eakat2/Checkers-Playing-Robot/Hardware/CAD/Board/Frames/Frame 2.SLDPRT

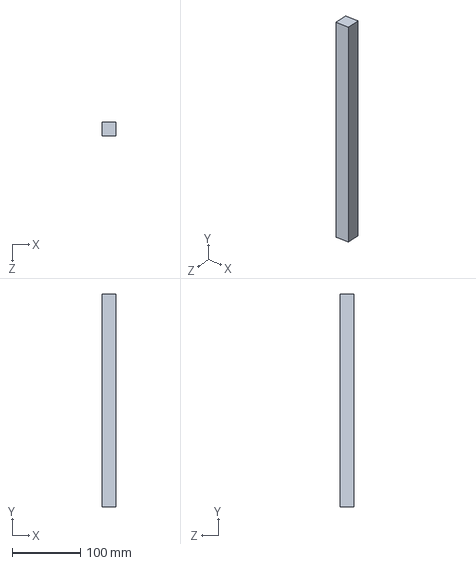
[picture p19: CAD file, 2021-05-21]
Hardware/CAD/Board/Frames/Frame 2.SLDPRT
20.0 x 311.0 x 20.0 mm
