eakat2/Checkers-Playing-Robot/Hardware/CAD/Board/Top.SLDPRT

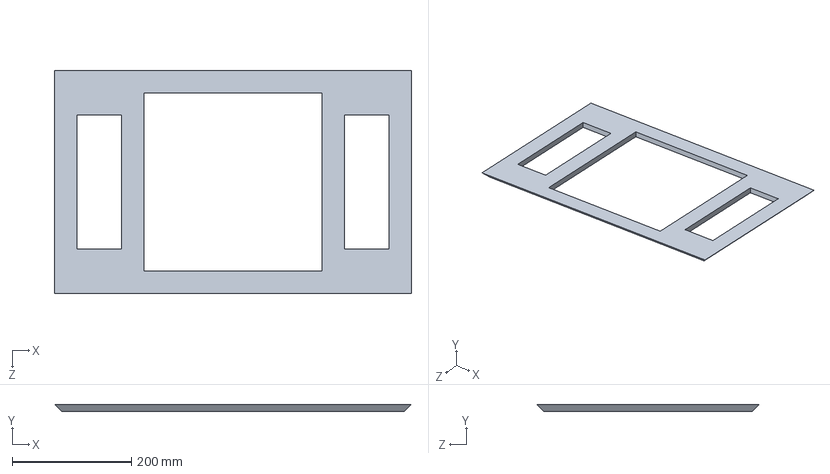
[picture p20: CAD file, 2021-05-21]
Hardware/CAD/Board/Top.SLDPRT
600.0 x 12.0 x 375.0 mm
