eakat2/Checkers-Playing-Robot/Hardware/CAD/Electromagnet.SLDPRT

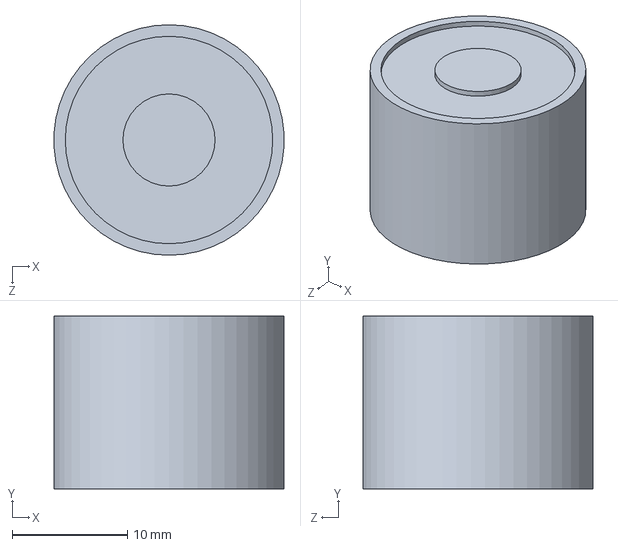
[picture p21: CAD file, 2021-01-19]
Hardware/CAD/Electromagnet.SLDPRT
20.0 x 15.0 x 20.0 mm
