eakat2/Checkers-Playing-Robot/Hardware/CAD/Arm/Base Bottom.SLDPRT

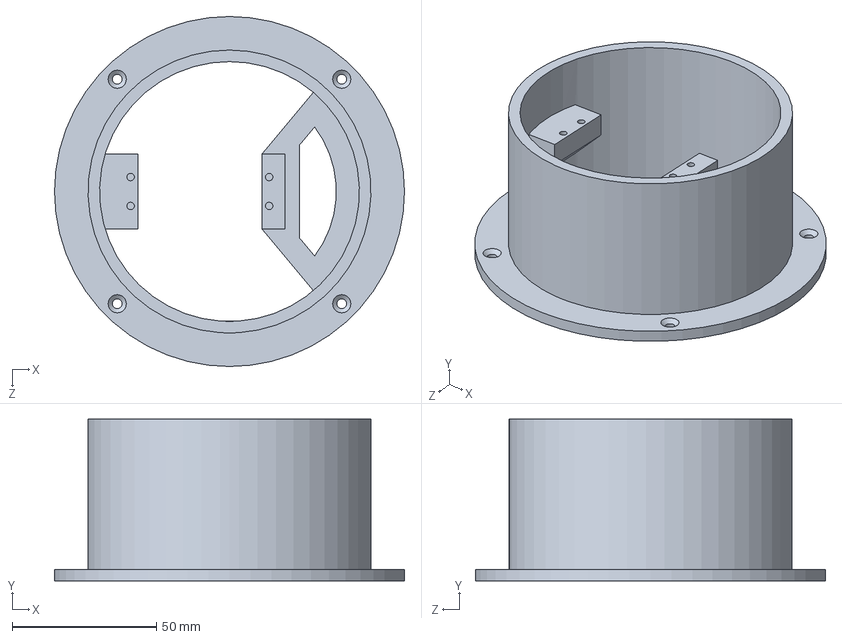
[picture p22: CAD file, 2021-05-28]
Hardware/CAD/Arm/Base Bottom.SLDPRT
121.2 x 56.0 x 121.2 mm
