eakat2/Checkers-Playing-Robot/Hardware/CAD/Arm/End Effector.SLDPRT

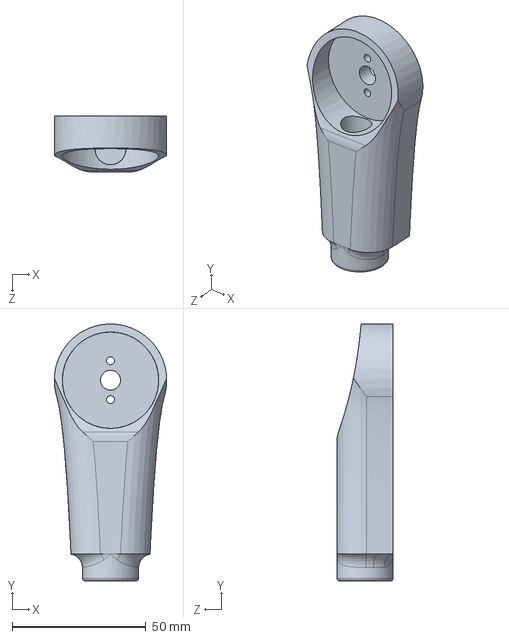
[picture p23: CAD file, 2021-05-28]
Hardware/CAD/Arm/End Effector.SLDPRT
42.0 x 96.0 x 21.0 mm
