eakat2/Checkers-Playing-Robot/Hardware/CAD/Board/Piece Draw.SLDPRT

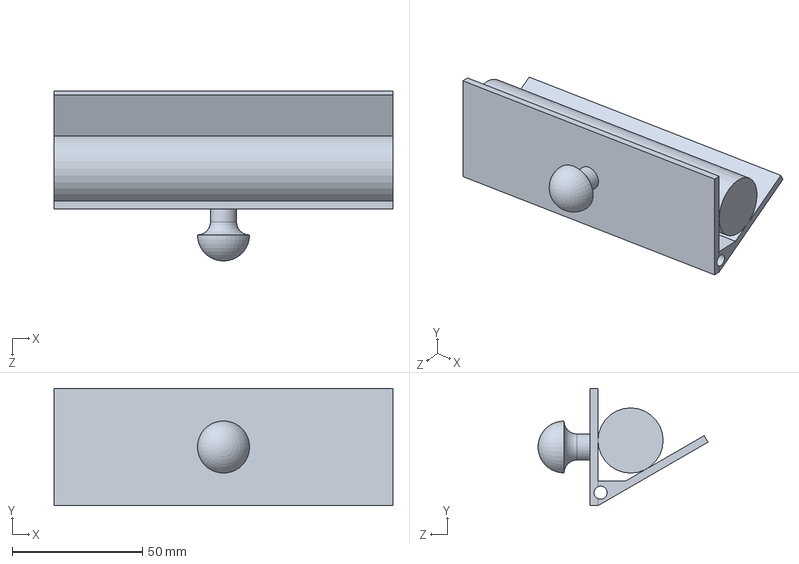
[picture p24: CAD file, 2021-05-21]
Hardware/CAD/Board/Piece Draw.SLDPRT
130.0 x 45.0 x 65.2 mm
