eakat2/Checkers-Playing-Robot/Hardware/CAD/Raspberry Pi/Microphone Plug, RPi4ModelB.SLDPRT

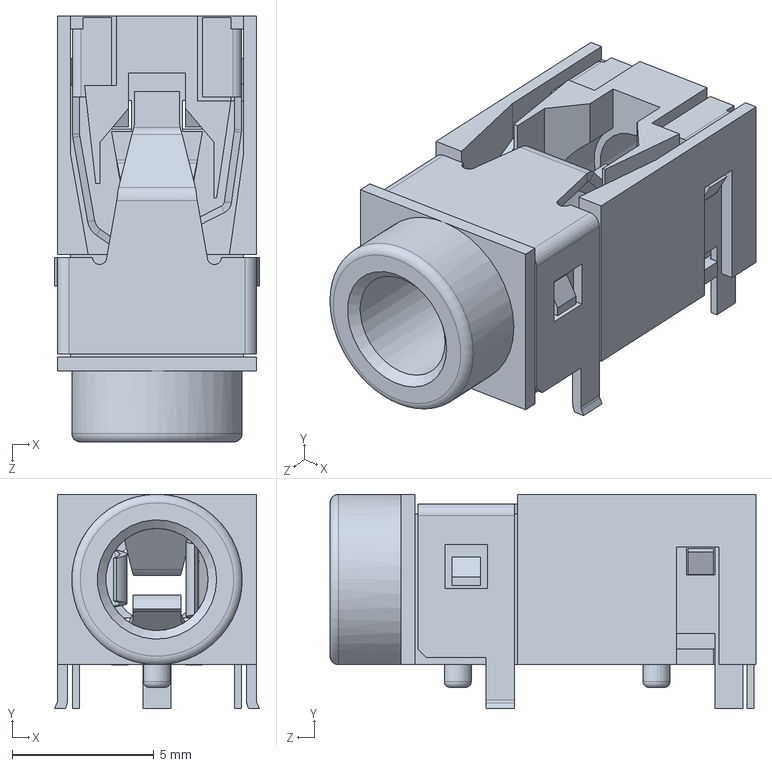
[picture p25: CAD file, 2021-01-19]
Hardware/CAD/Raspberry Pi/Microphone Plug, RPi4ModelB.SLDPRT
7.23 x 7.55 x 15.0 mm
