eakat2/Checkers-Playing-Robot/Hardware/CAD/Board/Front.SLDPRT

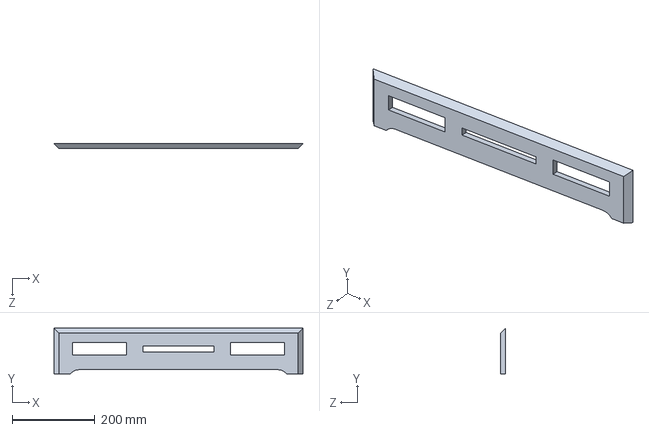
[picture p26: CAD file, 2021-05-21]
Hardware/CAD/Board/Front.SLDPRT
600.0 x 110.0 x 12.0 mm
