eakat2/Checkers-Playing-Robot/Hardware/CAD/Raspberry Pi/2.54 mm DUPONT MALE PIN HEADER, POE, 2X2, RPi4ModelB.SLDPRT

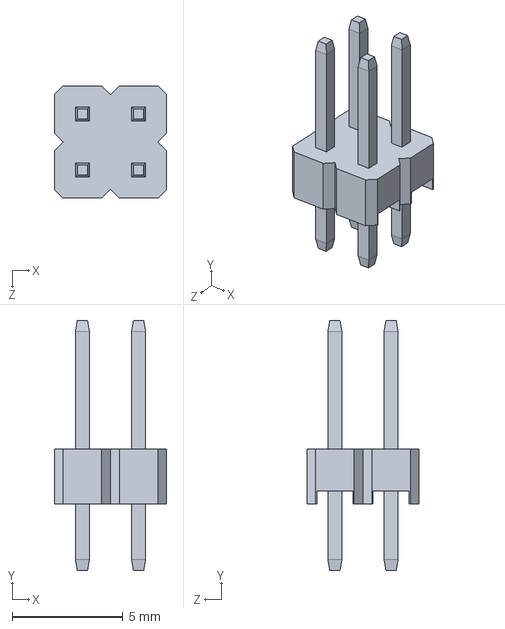
[picture p27: CAD file, 2021-01-19]
Hardware/CAD/Raspberry Pi/2.54 mm DUPONT MALE PIN HEADER, POE, 2X2, RPi4ModelB.SLDPRT
5.08 x 11.3 x 5.08 mm
