eakat2/Checkers-Playing-Robot/Hardware/CAD/Arm/Part 2.SLDPRT

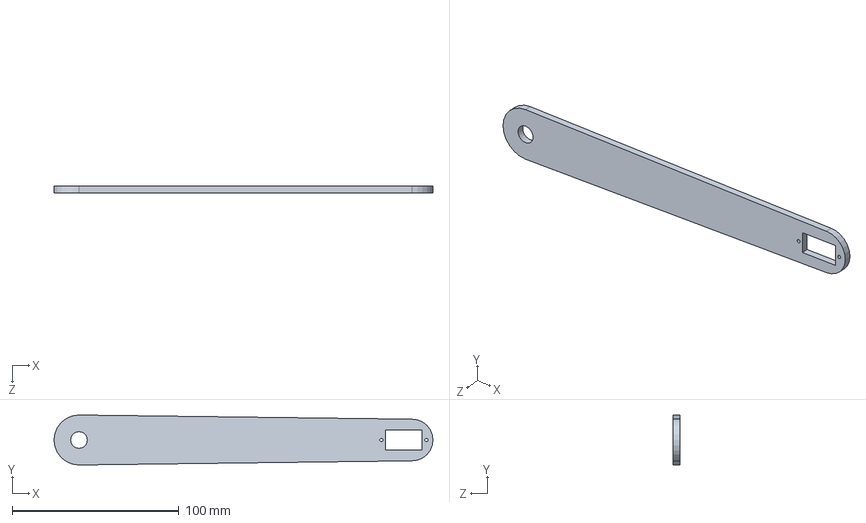
[picture p28: CAD file, 2021-05-21]
Hardware/CAD/Arm/Part 2.SLDPRT
227.5 x 30.0 x 4.00 mm
