eakat2/Checkers-Playing-Robot/Hardware/CAD/Board/Back.SLDPRT

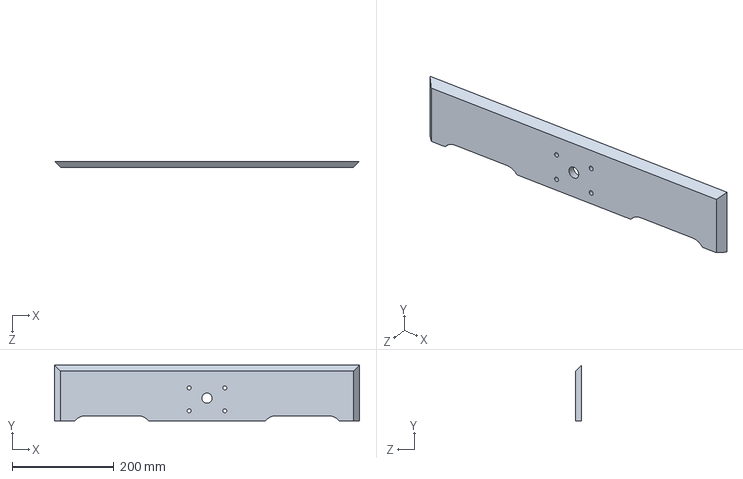
[picture p29: CAD file, 2021-05-21]
Hardware/CAD/Board/Back.SLDPRT
600.0 x 110.0 x 12.0 mm
