eakat2/Checkers-Playing-Robot/Hardware/CAD/Raspberry Pi/Female USB Type C Connector, RPi4ModelB.SLDPRT

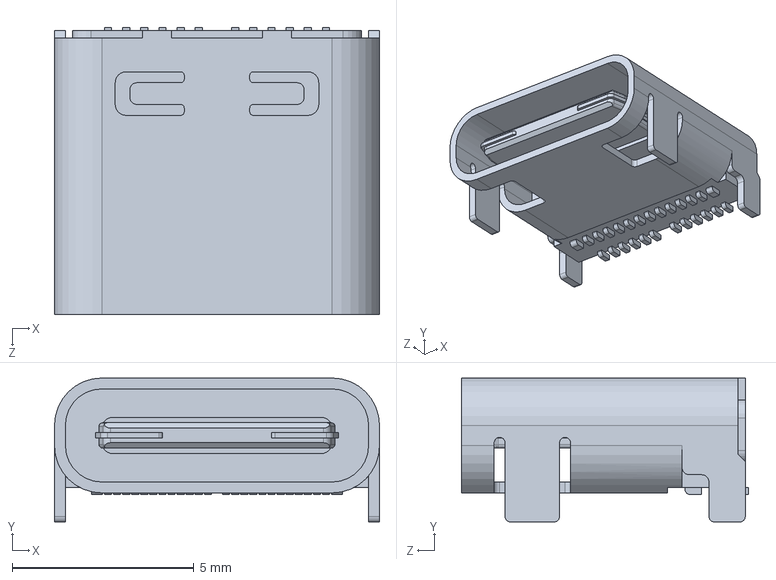
[picture p30: CAD file, 2021-01-19]
Hardware/CAD/Raspberry Pi/Female USB Type C Connector, RPi4ModelB.SLDPRT
8.94 x 3.96 x 7.90 mm
