eakat2/Checkers-Playing-Robot/Hardware/CAD/Arm/Base Top.SLDPRT

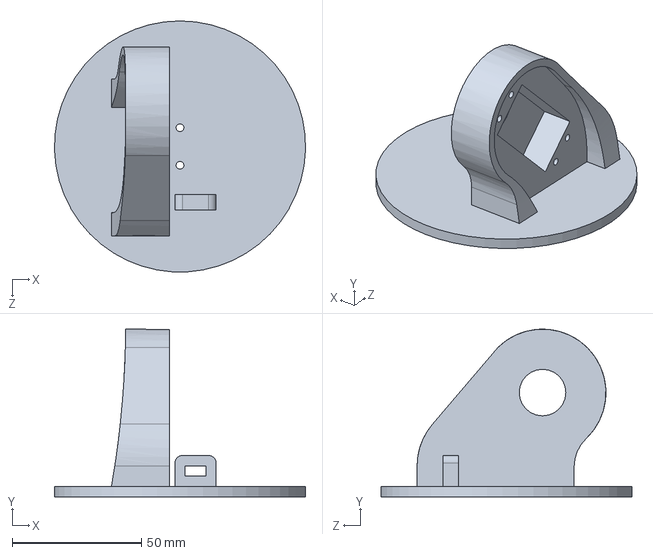
[picture p31: CAD file, 2021-05-21]
Hardware/CAD/Arm/Base Top.SLDPRT
97.0 x 64.8 x 97.0 mm
