eakat2/Checkers-Playing-Robot/Hardware/CAD/Raspberry Pi/2X USB2.0 PORTS, RPi4ModelB.SLDPRT

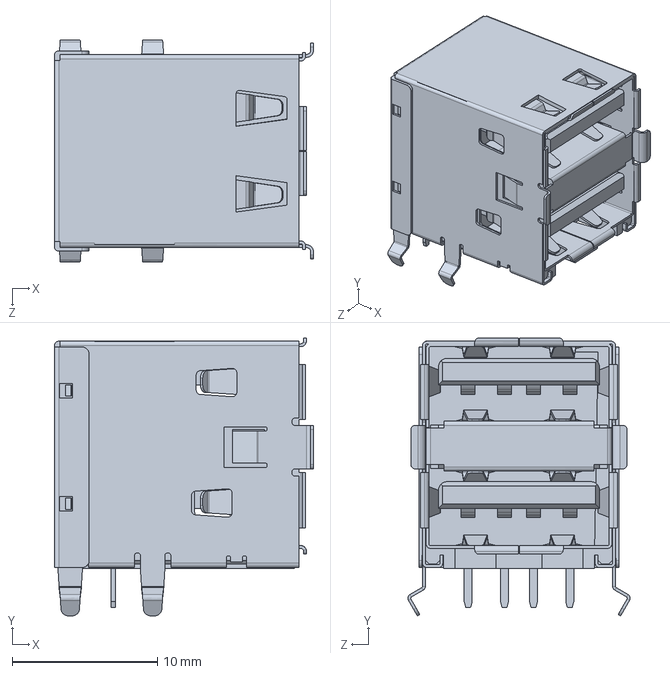
[picture p32: CAD file, 2021-01-19]
Hardware/CAD/Raspberry Pi/2X USB2.0 PORTS, RPi4ModelB.SLDPRT
17.9 x 19.2 x 15.3 mm
