eakat2/Checkers-Playing-Robot/Hardware/CAD/Arm/Part 4.SLDPRT

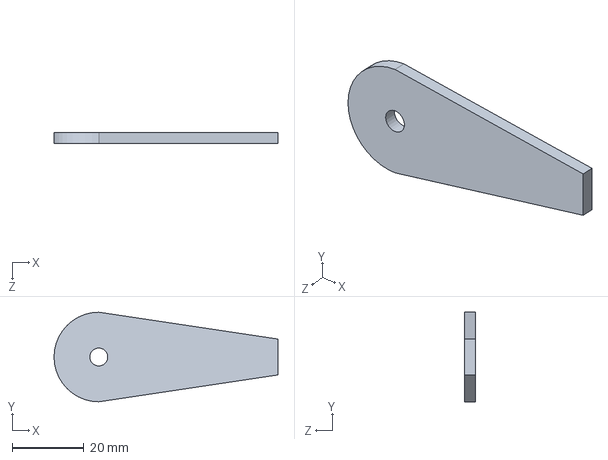
[picture p33: CAD file, 2021-05-21]
Hardware/CAD/Arm/Part 4.SLDPRT
62.5 x 25.0 x 3.00 mm
