eakat2/Checkers-Playing-Robot/Hardware/CAD/Raspberry Pi/Broadcom BCM54213PE Gigabit Ethernet Transceiver, RPi4ModelB.SLDPRT

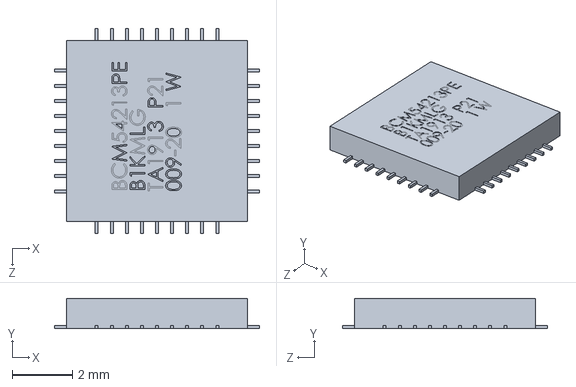
[picture p34: CAD file, 2021-01-19]
Hardware/CAD/Raspberry Pi/Broadcom BCM54213PE Gigabit Ethernet Transceiver, RPi4ModelB.SLDPRT
6.80 x 1.00 x 6.80 mm
