eakat2/Checkers-Playing-Robot/Hardware/CAD/Arm/Part 3.SLDPRT

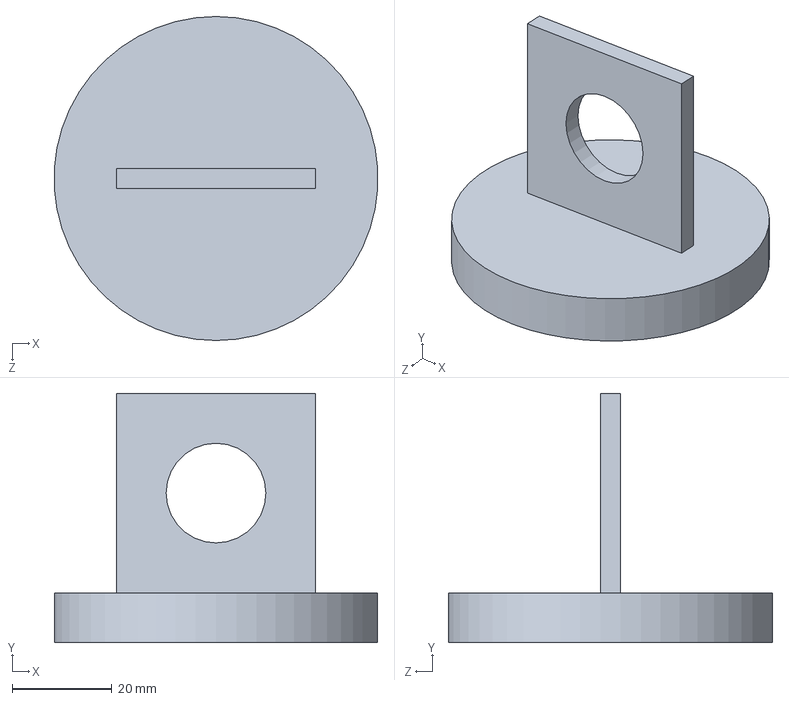
[picture p35: CAD file, 2021-05-21]
Hardware/CAD/Arm/Part 3.SLDPRT
64.9 x 50.0 x 65.0 mm
