eakat2/Checkers-Playing-Robot/Hardware/CAD/Arm/Part 1.SLDPRT

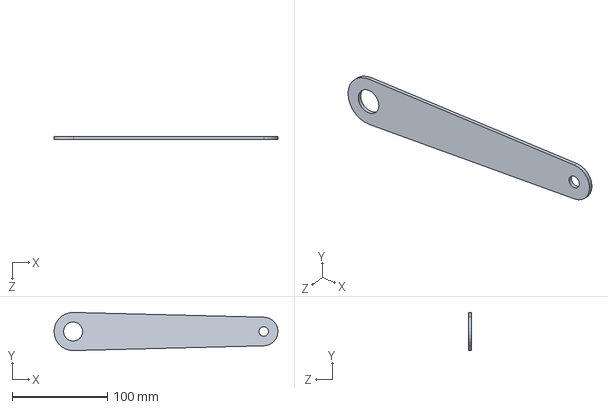
[picture p36: CAD file, 2021-05-21]
Hardware/CAD/Arm/Part 1.SLDPRT
235.0 x 40.0 x 3.00 mm
