eakat2/Checkers-Playing-Robot/Hardware/CAD/Raspberry Pi/2X USB3.0 PORTS, RPi4ModelB.SLDPRT

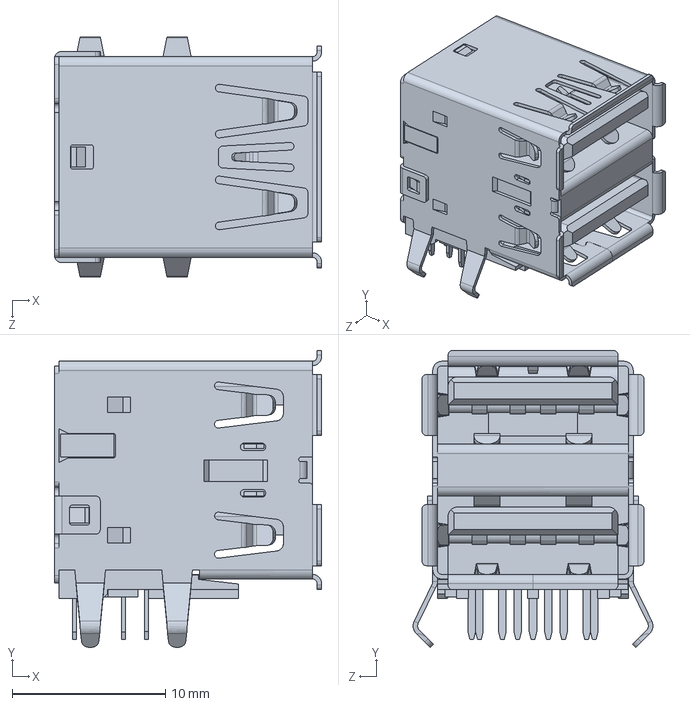
[picture p37: CAD file, 2021-01-19]
Hardware/CAD/Raspberry Pi/2X USB3.0 PORTS, RPi4ModelB.SLDPRT
17.5 x 19.4 x 15.7 mm
