eakat2/Checkers-Playing-Robot/Hardware/CAD/Arm/Spacer.SLDPRT

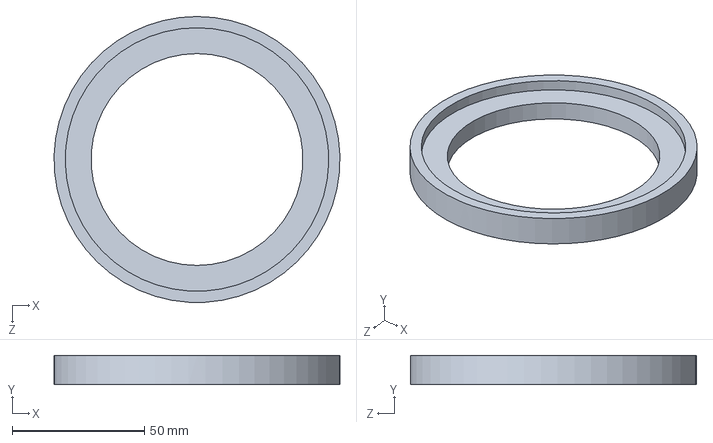
[picture p38: CAD file, 2021-05-21]
Hardware/CAD/Arm/Spacer.SLDPRT
108.0 x 11.0 x 108.0 mm
