eakat2/Checkers-Playing-Robot/Hardware/CAD/Arm/Arm Box.SLDPRT

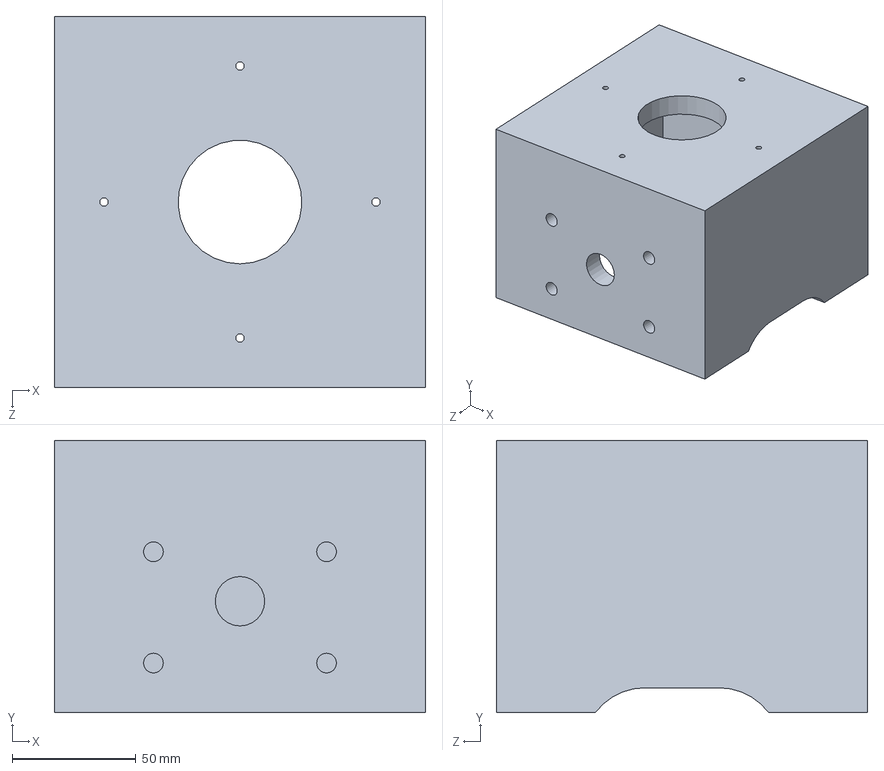
[picture p39: CAD file, 2021-05-21]
Hardware/CAD/Arm/Arm Box.SLDPRT
150.0 x 110.0 x 150.0 mm
