eakat2/Checkers-Playing-Robot/Hardware/CAD/Raspberry Pi/Cypress CYW43455 Wireless Module Cover, RPi4ModelB.SLDPRT

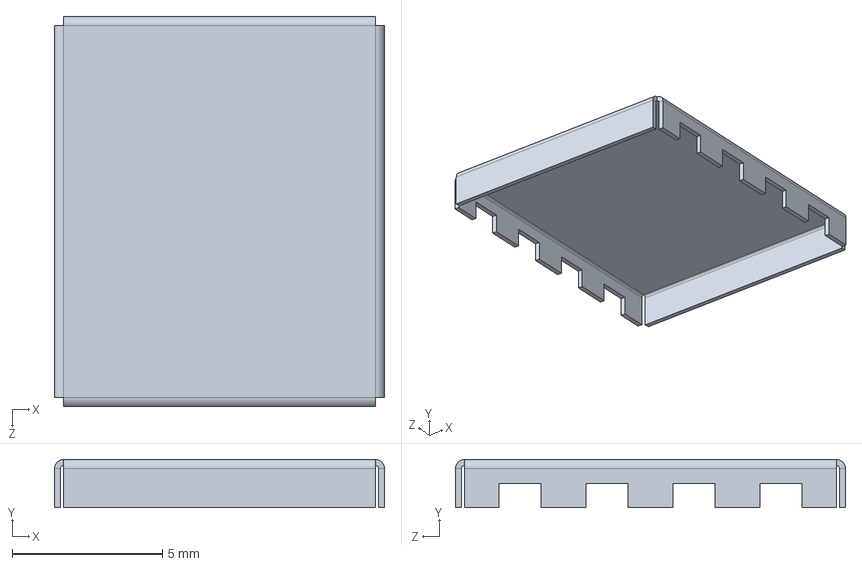
[picture p40: CAD file, 2021-01-19]
Hardware/CAD/Raspberry Pi/Cypress CYW43455 Wireless Module Cover, RPi4ModelB.SLDPRT
11.0 x 1.60 x 13.0 mm
