eakat2/Checkers-Playing-Robot/Hardware/CAD/Raspberry Pi/VIA VL805 PCIe USB 3.0 controller, RPi4ModelB.SLDPRT

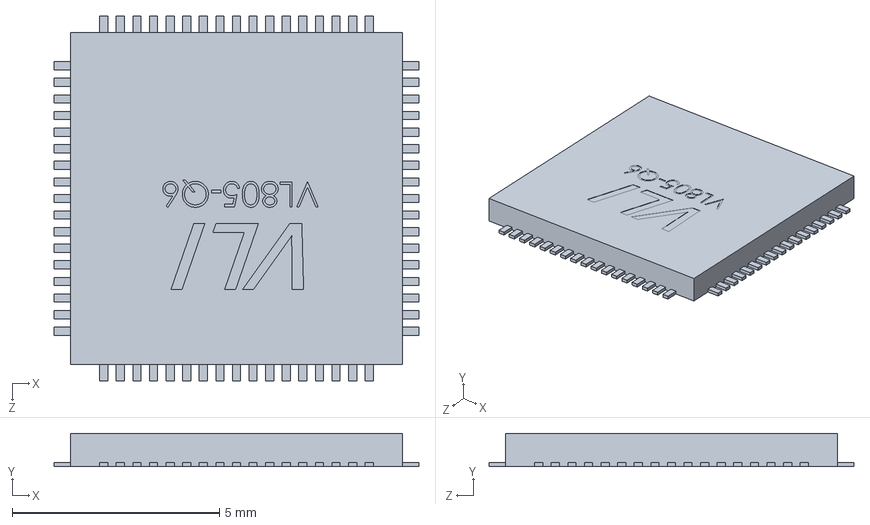
[picture p41: CAD file, 2021-01-19]
Hardware/CAD/Raspberry Pi/VIA VL805 PCIe USB 3.0 controller, RPi4ModelB.SLDPRT
8.80 x 0.8 x 8.80 mm
