eakat2/Checkers-Playing-Robot/Hardware/CAD/Raspberry Pi/Female Micro HDMI Connector, RPi4ModelB.SLDPRT

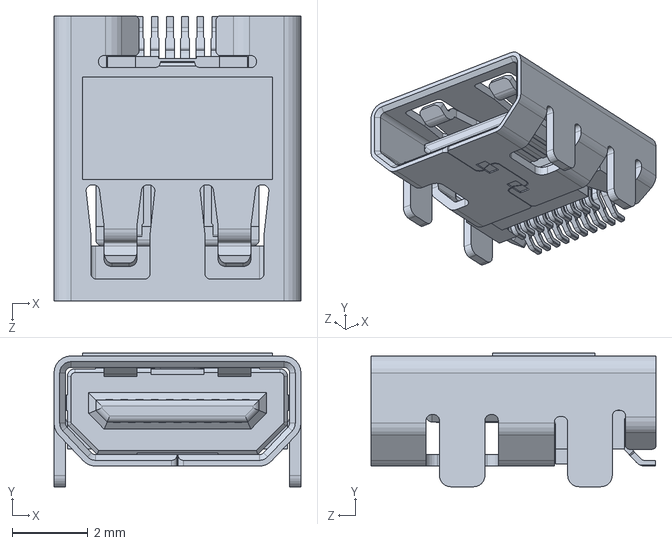
[picture p42: CAD file, 2021-01-19]
Hardware/CAD/Raspberry Pi/Female Micro HDMI Connector, RPi4ModelB.SLDPRT
6.50 x 3.52 x 7.50 mm
