eakat2/Checkers-Playing-Robot/Movement System/Game Piece Movement System.cydsn/codegentemp/Servo_4.h

/*******************************************************************************
* File Name: Servo_4.h  
* Version 2.20
*
* Description:
*  This file contains Pin function prototypes and register defines
*
* Note:
*
********************************************************************************
* Copyright 2008-2015, Cypress Semiconductor Corporation.  All rights reserved.
* You may use this file only in accordance with the license, terms, conditions, 
* disclaimers, and limitations in the end user license agreement accompanying 
* the software package with which this file was provided.
*******************************************************************************/

#if !defined(CY_PINS_Servo_4_H) /* Pins Servo_4_H */
#define CY_PINS_Servo_4_H

#include "cytypes.h"
#include "cyfitter.h"
#include "cypins.h"
#include "Servo_4_aliases.h"

/* APIs are not generated for P15[7:6] */
#if !(CY_PSOC5A &&\
	 Servo_4__PORT == 15 && ((Servo_4__MASK & 0xC0) != 0))


/***************************************
*        Function Prototypes             
***************************************/    

/**
* \addtogroup group_general
* @{
*/
void    Servo_4_Write(uint8 value);
void    Servo_4_SetDriveMode(uint8 mode);
uint8   Servo_4_ReadDataReg(void);
uint8   Servo_4_Read(void);
void    Servo_4_SetInterruptMode(uint16 position, uint16 mode);
uint8   Servo_4_ClearInterrupt(void);
/** @} general */

/***************************************
*           API Constants        
***************************************/
/**
* \addtogroup group_constants
* @{
*/
    /** \addtogroup driveMode Drive mode constants
     * \brief Constants to be passed as "mode" parameter in the Servo_4_SetDriveMode() function.
     *  @{
     */
        #define Servo_4_DM_ALG_HIZ         PIN_DM_ALG_HIZ
        #define Servo_4_DM_DIG_HIZ         PIN_DM_DIG_HIZ
        #define Servo_4_DM_RES_UP          PIN_DM_RES_UP
        #define Servo_4_DM_RES_DWN         PIN_DM_RES_DWN
        #define Servo_4_DM_OD_LO           PIN_DM_OD_LO
        #define Servo_4_DM_OD_HI           PIN_DM_OD_HI
        #define Servo_4_DM_STRONG          PIN_DM_STRONG
        #define Servo_4_DM_RES_UPDWN       PIN_DM_RES_UPDWN
    /** @} driveMode */
/** @} group_constants */
    
/* Digital Port Constants */
#define Servo_4_MASK               Servo_4__MASK
#define Servo_4_SHIFT              Servo_4__SHIFT
#define Servo_4_WIDTH              1u

/* Interrupt constants */
#if defined(Servo_4__INTSTAT)
/**
* \addtogroup group_constants
* @{
*/
    /** \addtogroup intrMode Interrupt constants
     * \brief Constants to be passed as "mode" parameter in Servo_4_SetInterruptMode() function.
     *  @{
     */
        #define Servo_4_INTR_NONE      (uint16)(0x0000u)
        #define Servo_4_INTR_RISING    (uint16)(0x0001u)
        #define Servo_4_INTR_FALLING   (uint16)(0x0002u)
        #define Servo_4_INTR_BOTH      (uint16)(0x0003u) 
    /** @} intrMode */
/** @} group_constants */

    #define Servo_4_INTR_MASK      (0x01u) 
#endif /* (Servo_4__INTSTAT) */


/***************************************
*             Registers        
***************************************/

/* Main Port Registers */
/* Pin State */
#define Servo_4_PS                     (* (reg8 *) Servo_4__PS)
/* Data Register */
#define Servo_4_DR                     (* (reg8 *) Servo_4__DR)
/* Port Number */
#define Servo_4_PRT_NUM                (* (reg8 *) Servo_4__PRT) 
/* Connect to Analog Globals */                                                  
#define Servo_4_AG                     (* (reg8 *) Servo_4__AG)                       
/* Analog MUX bux enable */
#define Servo_4_AMUX                   (* (reg8 *) Servo_4__AMUX) 
/* Bidirectional Enable */                                                        
#define Servo_4_BIE                    (* (reg8 *) Servo_4__BIE)
/* Bit-mask for Aliased Register Access */
#define Servo_4_BIT_MASK               (* (reg8 *) Servo_4__BIT_MASK)
/* Bypass Enable */
#define Servo_4_BYP                    (* (reg8 *) Servo_4__BYP)
/* Port wide control signals */                                                   
#define Servo_4_CTL                    (* (reg8 *) Servo_4__CTL)
/* Drive Modes */
#define Servo_4_DM0                    (* (reg8 *) Servo_4__DM0) 
#define Servo_4_DM1                    (* (reg8 *) Servo_4__DM1)
#define Servo_4_DM2                    (* (reg8 *) Servo_4__DM2) 
/* Input Buffer Disable Override */
#define Servo_4_INP_DIS                (* (reg8 *) Servo_4__INP_DIS)
/* LCD Common or Segment Drive */
#define Servo_4_LCD_COM_SEG            (* (reg8 *) Servo_4__LCD_COM_SEG)
/* Enable Segment LCD */
#define Servo_4_LCD_EN                 (* (reg8 *) Servo_4__LCD_EN)
/* Slew Rate Control */
#define Servo_4_SLW                    (* (reg8 *) Servo_4__SLW)

/* DSI Port Registers */
/* Global DSI Select Register */
#define Servo_4_PRTDSI__CAPS_SEL       (* (reg8 *) Servo_4__PRTDSI__CAPS_SEL) 
/* Double Sync Enable */
#define Servo_4_PRTDSI__DBL_SYNC_IN    (* (reg8 *) Servo_4__PRTDSI__DBL_SYNC_IN) 
/* Output Enable Select Drive Strength */
#define Servo_4_PRTDSI__OE_SEL0        (* (reg8 *) Servo_4__PRTDSI__OE_SEL0) 
#define Servo_4_PRTDSI__OE_SEL1        (* (reg8 *) Servo_4__PRTDSI__OE_SEL1) 
/* Port Pin Output Select Registers */
#define Servo_4_PRTDSI__OUT_SEL0       (* (reg8 *) Servo_4__PRTDSI__OUT_SEL0) 
#define Servo_4_PRTDSI__OUT_SEL1       (* (reg8 *) Servo_4__PRTDSI__OUT_SEL1) 
/* Sync Output Enable Registers */
#define Servo_4_PRTDSI__SYNC_OUT       (* (reg8 *) Servo_4__PRTDSI__SYNC_OUT) 

/* SIO registers */
#if defined(Servo_4__SIO_CFG)
    #define Servo_4_SIO_HYST_EN        (* (reg8 *) Servo_4__SIO_HYST_EN)
    #define Servo_4_SIO_REG_HIFREQ     (* (reg8 *) Servo_4__SIO_REG_HIFREQ)
    #define Servo_4_SIO_CFG            (* (reg8 *) Servo_4__SIO_CFG)
    #define Servo_4_SIO_DIFF           (* (reg8 *) Servo_4__SIO_DIFF)
#endif /* (Servo_4__SIO_CFG) */

/* Interrupt Registers */
#if defined(Servo_4__INTSTAT)
    #define Servo_4_INTSTAT            (* (reg8 *) Servo_4__INTSTAT)
    #define Servo_4_SNAP               (* (reg8 *) Servo_4__SNAP)
    
	#define Servo_4_0_INTTYPE_REG 		(* (reg8 *) Servo_4__0__INTTYPE)
#endif /* (Servo_4__INTSTAT) */

#endif /* CY_PSOC5A... */

#endif /*  CY_PINS_Servo_4_H */


/* [] END OF FILE */
