eakat2/Checkers-Playing-Robot/Movement System/Game Piece Movement System.cydsn/codegentemp/Servo_1_aliases.h

/*******************************************************************************
* File Name: Servo_1.h  
* Version 2.20
*
* Description:
*  This file contains the Alias definitions for Per-Pin APIs in cypins.h. 
*  Information on using these APIs can be found in the System Reference Guide.
*
* Note:
*
********************************************************************************
* Copyright 2008-2015, Cypress Semiconductor Corporation.  All rights reserved.
* You may use this file only in accordance with the license, terms, conditions, 
* disclaimers, and limitations in the end user license agreement accompanying 
* the software package with which this file was provided.
*******************************************************************************/

#if !defined(CY_PINS_Servo_1_ALIASES_H) /* Pins Servo_1_ALIASES_H */
#define CY_PINS_Servo_1_ALIASES_H

#include "cytypes.h"
#include "cyfitter.h"


/***************************************
*              Constants        
***************************************/
#define Servo_1_0			(Servo_1__0__PC)
#define Servo_1_0_INTR	((uint16)((uint16)0x0001u << Servo_1__0__SHIFT))

#define Servo_1_INTR_ALL	 ((uint16)(Servo_1_0_INTR))

#endif /* End Pins Servo_1_ALIASES_H */


/* [] END OF FILE */
