eakat2/Checkers-Playing-Robot/Movement System/Game Piece Movement System.cydsn/codegentemp/PWM_1.h

/*******************************************************************************
* File Name: PWM_1.h
* Version 3.30
*
* Description:
*  Contains the prototypes and constants for the functions available to the
*  PWM user module.
*
* Note:
*
********************************************************************************
* Copyright 2008-2014, Cypress Semiconductor Corporation.  All rights reserved.
* You may use this file only in accordance with the license, terms, conditions,
* disclaimers, and limitations in the end user license agreement accompanying
* the software package with which this file was provided.
********************************************************************************/

#if !defined(CY_PWM_PWM_1_H)
#define CY_PWM_PWM_1_H

#include "cyfitter.h"
#include "cytypes.h"
#include "CyLib.h" /* For CyEnterCriticalSection() and CyExitCriticalSection() functions */

extern uint8 PWM_1_initVar;


/***************************************
* Conditional Compilation Parameters
***************************************/
#define PWM_1_Resolution                     (16u)
#define PWM_1_UsingFixedFunction             (0u)
#define PWM_1_DeadBandMode                   (0u)
#define PWM_1_KillModeMinTime                (0u)
#define PWM_1_KillMode                       (0u)
#define PWM_1_PWMMode                        (0u)
#define PWM_1_PWMModeIsCenterAligned         (0u)
#define PWM_1_DeadBandUsed                   (0u)
#define PWM_1_DeadBand2_4                    (0u)

#if !defined(PWM_1_PWMUDB_genblk8_stsreg__REMOVED)
    #define PWM_1_UseStatus                  (1u)
#else
    #define PWM_1_UseStatus                  (0u)
#endif /* !defined(PWM_1_PWMUDB_genblk8_stsreg__REMOVED) */

#if !defined(PWM_1_PWMUDB_genblk1_ctrlreg__REMOVED)
    #define PWM_1_UseControl                 (1u)
#else
    #define PWM_1_UseControl                 (0u)
#endif /* !defined(PWM_1_PWMUDB_genblk1_ctrlreg__REMOVED) */

#define PWM_1_UseOneCompareMode              (1u)
#define PWM_1_MinimumKillTime                (1u)
#define PWM_1_EnableMode                     (0u)

#define PWM_1_CompareMode1SW                 (0u)
#define PWM_1_CompareMode2SW                 (0u)

/* Check to see if required defines such as CY_PSOC5LP are available */
/* They are defined starting with cy_boot v3.0 */
#if !defined (CY_PSOC5LP)
    #error Component PWM_v3_30 requires cy_boot v3.0 or later
#endif /* (CY_ PSOC5LP) */

/* Use Kill Mode Enumerated Types */
#define PWM_1__B_PWM__DISABLED 0
#define PWM_1__B_PWM__ASYNCHRONOUS 1
#define PWM_1__B_PWM__SINGLECYCLE 2
#define PWM_1__B_PWM__LATCHED 3
#define PWM_1__B_PWM__MINTIME 4


/* Use Dead Band Mode Enumerated Types */
#define PWM_1__B_PWM__DBMDISABLED 0
#define PWM_1__B_PWM__DBM_2_4_CLOCKS 1
#define PWM_1__B_PWM__DBM_256_CLOCKS 2


/* Used PWM Mode Enumerated Types */
#define PWM_1__B_PWM__ONE_OUTPUT 0
#define PWM_1__B_PWM__TWO_OUTPUTS 1
#define PWM_1__B_PWM__DUAL_EDGE 2
#define PWM_1__B_PWM__CENTER_ALIGN 3
#define PWM_1__B_PWM__DITHER 5
#define PWM_1__B_PWM__HARDWARESELECT 4


/* Used PWM Compare Mode Enumerated Types */
#define PWM_1__B_PWM__LESS_THAN 1
#define PWM_1__B_PWM__LESS_THAN_OR_EQUAL 2
#define PWM_1__B_PWM__GREATER_THAN 3
#define PWM_1__B_PWM__GREATER_THAN_OR_EQUAL_TO 4
#define PWM_1__B_PWM__EQUAL 0
#define PWM_1__B_PWM__FIRMWARE 5



/***************************************
* Data Struct Definition
***************************************/


/**************************************************************************
 * Sleep Wakeup Backup structure for PWM Component
 *************************************************************************/
typedef struct
{

    uint8 PWMEnableState;

    #if(!PWM_1_UsingFixedFunction)
        uint16 PWMUdb;               /* PWM Current Counter value  */
        #if(!PWM_1_PWMModeIsCenterAligned)
            uint16 PWMPeriod;
        #endif /* (!PWM_1_PWMModeIsCenterAligned) */
        #if (PWM_1_UseStatus)
            uint8 InterruptMaskValue;   /* PWM Current Interrupt Mask */
        #endif /* (PWM_1_UseStatus) */

        /* Backup for Deadband parameters */
        #if(PWM_1_DeadBandMode == PWM_1__B_PWM__DBM_256_CLOCKS || \
            PWM_1_DeadBandMode == PWM_1__B_PWM__DBM_2_4_CLOCKS)
            uint8 PWMdeadBandValue; /* Dead Band Counter Current Value */
        #endif /* deadband count is either 2-4 clocks or 256 clocks */

        /* Backup Kill Mode Counter*/
        #if(PWM_1_KillModeMinTime)
            uint8 PWMKillCounterPeriod; /* Kill Mode period value */
        #endif /* (PWM_1_KillModeMinTime) */

        /* Backup control register */
        #if(PWM_1_UseControl)
            uint8 PWMControlRegister; /* PWM Control Register value */
        #endif /* (PWM_1_UseControl) */

    #endif /* (!PWM_1_UsingFixedFunction) */

}PWM_1_backupStruct;


/***************************************
*        Function Prototypes
 **************************************/

void    PWM_1_Start(void) ;
void    PWM_1_Stop(void) ;

#if (PWM_1_UseStatus || PWM_1_UsingFixedFunction)
    void  PWM_1_SetInterruptMode(uint8 interruptMode) ;
    uint8 PWM_1_ReadStatusRegister(void) ;
#endif /* (PWM_1_UseStatus || PWM_1_UsingFixedFunction) */

#define PWM_1_GetInterruptSource() PWM_1_ReadStatusRegister()

#if (PWM_1_UseControl)
    uint8 PWM_1_ReadControlRegister(void) ;
    void  PWM_1_WriteControlRegister(uint8 control)
          ;
#endif /* (PWM_1_UseControl) */

#if (PWM_1_UseOneCompareMode)
   #if (PWM_1_CompareMode1SW)
       void    PWM_1_SetCompareMode(uint8 comparemode)
               ;
   #endif /* (PWM_1_CompareMode1SW) */
#else
    #if (PWM_1_CompareMode1SW)
        void    PWM_1_SetCompareMode1(uint8 comparemode)
                ;
    #endif /* (PWM_1_CompareMode1SW) */
    #if (PWM_1_CompareMode2SW)
        void    PWM_1_SetCompareMode2(uint8 comparemode)
                ;
    #endif /* (PWM_1_CompareMode2SW) */
#endif /* (PWM_1_UseOneCompareMode) */

#if (!PWM_1_UsingFixedFunction)
    uint16   PWM_1_ReadCounter(void) ;
    uint16 PWM_1_ReadCapture(void) ;

    #if (PWM_1_UseStatus)
            void PWM_1_ClearFIFO(void) ;
    #endif /* (PWM_1_UseStatus) */

    void    PWM_1_WriteCounter(uint16 counter)
            ;
#endif /* (!PWM_1_UsingFixedFunction) */

void    PWM_1_WritePeriod(uint16 period)
        ;
uint16 PWM_1_ReadPeriod(void) ;

#if (PWM_1_UseOneCompareMode)
    void    PWM_1_WriteCompare(uint16 compare)
            ;
    uint16 PWM_1_ReadCompare(void) ;
#else
    void    PWM_1_WriteCompare1(uint16 compare)
            ;
    uint16 PWM_1_ReadCompare1(void) ;
    void    PWM_1_WriteCompare2(uint16 compare)
            ;
    uint16 PWM_1_ReadCompare2(void) ;
#endif /* (PWM_1_UseOneCompareMode) */


#if (PWM_1_DeadBandUsed)
    void    PWM_1_WriteDeadTime(uint8 deadtime) ;
    uint8   PWM_1_ReadDeadTime(void) ;
#endif /* (PWM_1_DeadBandUsed) */

#if ( PWM_1_KillModeMinTime)
    void PWM_1_WriteKillTime(uint8 killtime) ;
    uint8 PWM_1_ReadKillTime(void) ;
#endif /* ( PWM_1_KillModeMinTime) */

void PWM_1_Init(void) ;
void PWM_1_Enable(void) ;
void PWM_1_Sleep(void) ;
void PWM_1_Wakeup(void) ;
void PWM_1_SaveConfig(void) ;
void PWM_1_RestoreConfig(void) ;


/***************************************
*         Initialization Values
**************************************/
#define PWM_1_INIT_PERIOD_VALUE          (39999u)
#define PWM_1_INIT_COMPARE_VALUE1        (2000u)
#define PWM_1_INIT_COMPARE_VALUE2        (63u)
#define PWM_1_INIT_INTERRUPTS_MODE       (uint8)(((uint8)(0u <<   \
                                                    PWM_1_STATUS_TC_INT_EN_MASK_SHIFT)) | \
                                                    (uint8)((uint8)(0u <<  \
                                                    PWM_1_STATUS_CMP2_INT_EN_MASK_SHIFT)) | \
                                                    (uint8)((uint8)(0u <<  \
                                                    PWM_1_STATUS_CMP1_INT_EN_MASK_SHIFT )) | \
                                                    (uint8)((uint8)(0u <<  \
                                                    PWM_1_STATUS_KILL_INT_EN_MASK_SHIFT )))
#define PWM_1_DEFAULT_COMPARE2_MODE      (uint8)((uint8)1u <<  PWM_1_CTRL_CMPMODE2_SHIFT)
#define PWM_1_DEFAULT_COMPARE1_MODE      (uint8)((uint8)1u <<  PWM_1_CTRL_CMPMODE1_SHIFT)
#define PWM_1_INIT_DEAD_TIME             (1u)


/********************************
*         Registers
******************************** */

#if (PWM_1_UsingFixedFunction)
   #define PWM_1_PERIOD_LSB              (*(reg16 *) PWM_1_PWMHW__PER0)
   #define PWM_1_PERIOD_LSB_PTR          ( (reg16 *) PWM_1_PWMHW__PER0)
   #define PWM_1_COMPARE1_LSB            (*(reg16 *) PWM_1_PWMHW__CNT_CMP0)
   #define PWM_1_COMPARE1_LSB_PTR        ( (reg16 *) PWM_1_PWMHW__CNT_CMP0)
   #define PWM_1_COMPARE2_LSB            (0x00u)
   #define PWM_1_COMPARE2_LSB_PTR        (0x00u)
   #define PWM_1_COUNTER_LSB             (*(reg16 *) PWM_1_PWMHW__CNT_CMP0)
   #define PWM_1_COUNTER_LSB_PTR         ( (reg16 *) PWM_1_PWMHW__CNT_CMP0)
   #define PWM_1_CAPTURE_LSB             (*(reg16 *) PWM_1_PWMHW__CAP0)
   #define PWM_1_CAPTURE_LSB_PTR         ( (reg16 *) PWM_1_PWMHW__CAP0)
   #define PWM_1_RT1                     (*(reg8 *)  PWM_1_PWMHW__RT1)
   #define PWM_1_RT1_PTR                 ( (reg8 *)  PWM_1_PWMHW__RT1)

#else
   #if (PWM_1_Resolution == 8u) /* 8bit - PWM */

       #if(PWM_1_PWMModeIsCenterAligned)
           #define PWM_1_PERIOD_LSB      (*(reg8 *)  PWM_1_PWMUDB_sP16_pwmdp_u0__D1_REG)
           #define PWM_1_PERIOD_LSB_PTR  ((reg8 *)   PWM_1_PWMUDB_sP16_pwmdp_u0__D1_REG)
       #else
           #define PWM_1_PERIOD_LSB      (*(reg8 *)  PWM_1_PWMUDB_sP16_pwmdp_u0__F0_REG)
           #define PWM_1_PERIOD_LSB_PTR  ((reg8 *)   PWM_1_PWMUDB_sP16_pwmdp_u0__F0_REG)
       #endif /* (PWM_1_PWMModeIsCenterAligned) */

       #define PWM_1_COMPARE1_LSB        (*(reg8 *)  PWM_1_PWMUDB_sP16_pwmdp_u0__D0_REG)
       #define PWM_1_COMPARE1_LSB_PTR    ((reg8 *)   PWM_1_PWMUDB_sP16_pwmdp_u0__D0_REG)
       #define PWM_1_COMPARE2_LSB        (*(reg8 *)  PWM_1_PWMUDB_sP16_pwmdp_u0__D1_REG)
       #define PWM_1_COMPARE2_LSB_PTR    ((reg8 *)   PWM_1_PWMUDB_sP16_pwmdp_u0__D1_REG)
       #define PWM_1_COUNTERCAP_LSB      (*(reg8 *)  PWM_1_PWMUDB_sP16_pwmdp_u0__A1_REG)
       #define PWM_1_COUNTERCAP_LSB_PTR  ((reg8 *)   PWM_1_PWMUDB_sP16_pwmdp_u0__A1_REG)
       #define PWM_1_COUNTER_LSB         (*(reg8 *)  PWM_1_PWMUDB_sP16_pwmdp_u0__A0_REG)
       #define PWM_1_COUNTER_LSB_PTR     ((reg8 *)   PWM_1_PWMUDB_sP16_pwmdp_u0__A0_REG)
       #define PWM_1_CAPTURE_LSB         (*(reg8 *)  PWM_1_PWMUDB_sP16_pwmdp_u0__F1_REG)
       #define PWM_1_CAPTURE_LSB_PTR     ((reg8 *)   PWM_1_PWMUDB_sP16_pwmdp_u0__F1_REG)

   #else
        #if(CY_PSOC3) /* 8-bit address space */
            #if(PWM_1_PWMModeIsCenterAligned)
               #define PWM_1_PERIOD_LSB      (*(reg16 *) PWM_1_PWMUDB_sP16_pwmdp_u0__D1_REG)
               #define PWM_1_PERIOD_LSB_PTR  ((reg16 *)  PWM_1_PWMUDB_sP16_pwmdp_u0__D1_REG)
            #else
               #define PWM_1_PERIOD_LSB      (*(reg16 *) PWM_1_PWMUDB_sP16_pwmdp_u0__F0_REG)
               #define PWM_1_PERIOD_LSB_PTR  ((reg16 *)  PWM_1_PWMUDB_sP16_pwmdp_u0__F0_REG)
            #endif /* (PWM_1_PWMModeIsCenterAligned) */

            #define PWM_1_COMPARE1_LSB       (*(reg16 *) PWM_1_PWMUDB_sP16_pwmdp_u0__D0_REG)
            #define PWM_1_COMPARE1_LSB_PTR   ((reg16 *)  PWM_1_PWMUDB_sP16_pwmdp_u0__D0_REG)
            #define PWM_1_COMPARE2_LSB       (*(reg16 *) PWM_1_PWMUDB_sP16_pwmdp_u0__D1_REG)
            #define PWM_1_COMPARE2_LSB_PTR   ((reg16 *)  PWM_1_PWMUDB_sP16_pwmdp_u0__D1_REG)
            #define PWM_1_COUNTERCAP_LSB     (*(reg16 *) PWM_1_PWMUDB_sP16_pwmdp_u0__A1_REG)
            #define PWM_1_COUNTERCAP_LSB_PTR ((reg16 *)  PWM_1_PWMUDB_sP16_pwmdp_u0__A1_REG)
            #define PWM_1_COUNTER_LSB        (*(reg16 *) PWM_1_PWMUDB_sP16_pwmdp_u0__A0_REG)
            #define PWM_1_COUNTER_LSB_PTR    ((reg16 *)  PWM_1_PWMUDB_sP16_pwmdp_u0__A0_REG)
            #define PWM_1_CAPTURE_LSB        (*(reg16 *) PWM_1_PWMUDB_sP16_pwmdp_u0__F1_REG)
            #define PWM_1_CAPTURE_LSB_PTR    ((reg16 *)  PWM_1_PWMUDB_sP16_pwmdp_u0__F1_REG)
        #else
            #if(PWM_1_PWMModeIsCenterAligned)
               #define PWM_1_PERIOD_LSB      (*(reg16 *) PWM_1_PWMUDB_sP16_pwmdp_u0__16BIT_D1_REG)
               #define PWM_1_PERIOD_LSB_PTR  ((reg16 *)  PWM_1_PWMUDB_sP16_pwmdp_u0__16BIT_D1_REG)
            #else
               #define PWM_1_PERIOD_LSB      (*(reg16 *) PWM_1_PWMUDB_sP16_pwmdp_u0__16BIT_F0_REG)
               #define PWM_1_PERIOD_LSB_PTR  ((reg16 *)  PWM_1_PWMUDB_sP16_pwmdp_u0__16BIT_F0_REG)
            #endif /* (PWM_1_PWMModeIsCenterAligned) */

            #define PWM_1_COMPARE1_LSB       (*(reg16 *) PWM_1_PWMUDB_sP16_pwmdp_u0__16BIT_D0_REG)
            #define PWM_1_COMPARE1_LSB_PTR   ((reg16 *)  PWM_1_PWMUDB_sP16_pwmdp_u0__16BIT_D0_REG)
            #define PWM_1_COMPARE2_LSB       (*(reg16 *) PWM_1_PWMUDB_sP16_pwmdp_u0__16BIT_D1_REG)
            #define PWM_1_COMPARE2_LSB_PTR   ((reg16 *)  PWM_1_PWMUDB_sP16_pwmdp_u0__16BIT_D1_REG)
            #define PWM_1_COUNTERCAP_LSB     (*(reg16 *) PWM_1_PWMUDB_sP16_pwmdp_u0__16BIT_A1_REG)
            #define PWM_1_COUNTERCAP_LSB_PTR ((reg16 *)  PWM_1_PWMUDB_sP16_pwmdp_u0__16BIT_A1_REG)
            #define PWM_1_COUNTER_LSB        (*(reg16 *) PWM_1_PWMUDB_sP16_pwmdp_u0__16BIT_A0_REG)
            #define PWM_1_COUNTER_LSB_PTR    ((reg16 *)  PWM_1_PWMUDB_sP16_pwmdp_u0__16BIT_A0_REG)
            #define PWM_1_CAPTURE_LSB        (*(reg16 *) PWM_1_PWMUDB_sP16_pwmdp_u0__16BIT_F1_REG)
            #define PWM_1_CAPTURE_LSB_PTR    ((reg16 *)  PWM_1_PWMUDB_sP16_pwmdp_u0__16BIT_F1_REG)
        #endif /* (CY_PSOC3) */

       #define PWM_1_AUX_CONTROLDP1          (*(reg8 *)  PWM_1_PWMUDB_sP16_pwmdp_u1__DP_AUX_CTL_REG)
       #define PWM_1_AUX_CONTROLDP1_PTR      ((reg8 *)   PWM_1_PWMUDB_sP16_pwmdp_u1__DP_AUX_CTL_REG)

   #endif /* (PWM_1_Resolution == 8) */

   #define PWM_1_COUNTERCAP_LSB_PTR_8BIT ( (reg8 *)  PWM_1_PWMUDB_sP16_pwmdp_u0__A1_REG)
   #define PWM_1_AUX_CONTROLDP0          (*(reg8 *)  PWM_1_PWMUDB_sP16_pwmdp_u0__DP_AUX_CTL_REG)
   #define PWM_1_AUX_CONTROLDP0_PTR      ((reg8 *)   PWM_1_PWMUDB_sP16_pwmdp_u0__DP_AUX_CTL_REG)

#endif /* (PWM_1_UsingFixedFunction) */

#if(PWM_1_KillModeMinTime )
    #define PWM_1_KILLMODEMINTIME        (*(reg8 *)  PWM_1_PWMUDB_sKM_killmodecounterdp_u0__D0_REG)
    #define PWM_1_KILLMODEMINTIME_PTR    ((reg8 *)   PWM_1_PWMUDB_sKM_killmodecounterdp_u0__D0_REG)
    /* Fixed Function Block has no Kill Mode parameters because it is Asynchronous only */
#endif /* (PWM_1_KillModeMinTime ) */

#if(PWM_1_DeadBandMode == PWM_1__B_PWM__DBM_256_CLOCKS)
    #define PWM_1_DEADBAND_COUNT         (*(reg8 *)  PWM_1_PWMUDB_sDB255_deadbandcounterdp_u0__D0_REG)
    #define PWM_1_DEADBAND_COUNT_PTR     ((reg8 *)   PWM_1_PWMUDB_sDB255_deadbandcounterdp_u0__D0_REG)
    #define PWM_1_DEADBAND_LSB_PTR       ((reg8 *)   PWM_1_PWMUDB_sDB255_deadbandcounterdp_u0__A0_REG)
    #define PWM_1_DEADBAND_LSB           (*(reg8 *)  PWM_1_PWMUDB_sDB255_deadbandcounterdp_u0__A0_REG)
#elif(PWM_1_DeadBandMode == PWM_1__B_PWM__DBM_2_4_CLOCKS)
    
    /* In Fixed Function Block these bits are in the control blocks control register */
    #if (PWM_1_UsingFixedFunction)
        #define PWM_1_DEADBAND_COUNT         (*(reg8 *)  PWM_1_PWMHW__CFG0)
        #define PWM_1_DEADBAND_COUNT_PTR     ((reg8 *)   PWM_1_PWMHW__CFG0)
        #define PWM_1_DEADBAND_COUNT_MASK    (uint8)((uint8)0x03u << PWM_1_DEADBAND_COUNT_SHIFT)

        /* As defined by the Register Map as DEADBAND_PERIOD[1:0] in CFG0 */
        #define PWM_1_DEADBAND_COUNT_SHIFT   (0x06u)
    #else
        /* Lower two bits of the added control register define the count 1-3 */
        #define PWM_1_DEADBAND_COUNT         (*(reg8 *)  PWM_1_PWMUDB_genblk7_dbctrlreg__CONTROL_REG)
        #define PWM_1_DEADBAND_COUNT_PTR     ((reg8 *)   PWM_1_PWMUDB_genblk7_dbctrlreg__CONTROL_REG)
        #define PWM_1_DEADBAND_COUNT_MASK    (uint8)((uint8)0x03u << PWM_1_DEADBAND_COUNT_SHIFT)

        /* As defined by the verilog implementation of the Control Register */
        #define PWM_1_DEADBAND_COUNT_SHIFT   (0x00u)
    #endif /* (PWM_1_UsingFixedFunction) */
#endif /* (PWM_1_DeadBandMode == PWM_1__B_PWM__DBM_256_CLOCKS) */



#if (PWM_1_UsingFixedFunction)
    #define PWM_1_STATUS                 (*(reg8 *) PWM_1_PWMHW__SR0)
    #define PWM_1_STATUS_PTR             ((reg8 *) PWM_1_PWMHW__SR0)
    #define PWM_1_STATUS_MASK            (*(reg8 *) PWM_1_PWMHW__SR0)
    #define PWM_1_STATUS_MASK_PTR        ((reg8 *) PWM_1_PWMHW__SR0)
    #define PWM_1_CONTROL                (*(reg8 *) PWM_1_PWMHW__CFG0)
    #define PWM_1_CONTROL_PTR            ((reg8 *) PWM_1_PWMHW__CFG0)
    #define PWM_1_CONTROL2               (*(reg8 *) PWM_1_PWMHW__CFG1)
    #define PWM_1_CONTROL3               (*(reg8 *) PWM_1_PWMHW__CFG2)
    #define PWM_1_GLOBAL_ENABLE          (*(reg8 *) PWM_1_PWMHW__PM_ACT_CFG)
    #define PWM_1_GLOBAL_ENABLE_PTR      ( (reg8 *) PWM_1_PWMHW__PM_ACT_CFG)
    #define PWM_1_GLOBAL_STBY_ENABLE     (*(reg8 *) PWM_1_PWMHW__PM_STBY_CFG)
    #define PWM_1_GLOBAL_STBY_ENABLE_PTR ( (reg8 *) PWM_1_PWMHW__PM_STBY_CFG)


    /***********************************
    *          Constants
    ***********************************/

    /* Fixed Function Block Chosen */
    #define PWM_1_BLOCK_EN_MASK          (PWM_1_PWMHW__PM_ACT_MSK)
    #define PWM_1_BLOCK_STBY_EN_MASK     (PWM_1_PWMHW__PM_STBY_MSK)
    
    /* Control Register definitions */
    #define PWM_1_CTRL_ENABLE_SHIFT      (0x00u)

    /* As defined by Register map as MODE_CFG bits in CFG2*/
    #define PWM_1_CTRL_CMPMODE1_SHIFT    (0x04u)

    /* As defined by Register map */
    #define PWM_1_CTRL_DEAD_TIME_SHIFT   (0x06u)  

    /* Fixed Function Block Only CFG register bit definitions */
    /*  Set to compare mode */
    #define PWM_1_CFG0_MODE              (0x02u)   

    /* Enable the block to run */
    #define PWM_1_CFG0_ENABLE            (0x01u)   
    
    /* As defined by Register map as DB bit in CFG0 */
    #define PWM_1_CFG0_DB                (0x20u)   

    /* Control Register Bit Masks */
    #define PWM_1_CTRL_ENABLE            (uint8)((uint8)0x01u << PWM_1_CTRL_ENABLE_SHIFT)
    #define PWM_1_CTRL_RESET             (uint8)((uint8)0x01u << PWM_1_CTRL_RESET_SHIFT)
    #define PWM_1_CTRL_CMPMODE2_MASK     (uint8)((uint8)0x07u << PWM_1_CTRL_CMPMODE2_SHIFT)
    #define PWM_1_CTRL_CMPMODE1_MASK     (uint8)((uint8)0x07u << PWM_1_CTRL_CMPMODE1_SHIFT)

    /* Control2 Register Bit Masks */
    /* As defined in Register Map, Part of the TMRX_CFG1 register */
    #define PWM_1_CTRL2_IRQ_SEL_SHIFT    (0x00u)
    #define PWM_1_CTRL2_IRQ_SEL          (uint8)((uint8)0x01u << PWM_1_CTRL2_IRQ_SEL_SHIFT)

    /* Status Register Bit Locations */
    /* As defined by Register map as TC in SR0 */
    #define PWM_1_STATUS_TC_SHIFT        (0x07u)   
    
    /* As defined by the Register map as CAP_CMP in SR0 */
    #define PWM_1_STATUS_CMP1_SHIFT      (0x06u)   

    /* Status Register Interrupt Enable Bit Locations */
    #define PWM_1_STATUS_KILL_INT_EN_MASK_SHIFT          (0x00u)
    #define PWM_1_STATUS_TC_INT_EN_MASK_SHIFT            (PWM_1_STATUS_TC_SHIFT - 4u)
    #define PWM_1_STATUS_CMP2_INT_EN_MASK_SHIFT          (0x00u)
    #define PWM_1_STATUS_CMP1_INT_EN_MASK_SHIFT          (PWM_1_STATUS_CMP1_SHIFT - 4u)

    /* Status Register Bit Masks */
    #define PWM_1_STATUS_TC              (uint8)((uint8)0x01u << PWM_1_STATUS_TC_SHIFT)
    #define PWM_1_STATUS_CMP1            (uint8)((uint8)0x01u << PWM_1_STATUS_CMP1_SHIFT)

    /* Status Register Interrupt Bit Masks */
    #define PWM_1_STATUS_TC_INT_EN_MASK              (uint8)((uint8)PWM_1_STATUS_TC >> 4u)
    #define PWM_1_STATUS_CMP1_INT_EN_MASK            (uint8)((uint8)PWM_1_STATUS_CMP1 >> 4u)

    /*RT1 Synch Constants */
    #define PWM_1_RT1_SHIFT             (0x04u)

    /* Sync TC and CMP bit masks */
    #define PWM_1_RT1_MASK              (uint8)((uint8)0x03u << PWM_1_RT1_SHIFT)
    #define PWM_1_SYNC                  (uint8)((uint8)0x03u << PWM_1_RT1_SHIFT)
    #define PWM_1_SYNCDSI_SHIFT         (0x00u)

    /* Sync all DSI inputs */
    #define PWM_1_SYNCDSI_MASK          (uint8)((uint8)0x0Fu << PWM_1_SYNCDSI_SHIFT)

    /* Sync all DSI inputs */
    #define PWM_1_SYNCDSI_EN            (uint8)((uint8)0x0Fu << PWM_1_SYNCDSI_SHIFT)


#else
    #define PWM_1_STATUS                (*(reg8 *)   PWM_1_PWMUDB_genblk8_stsreg__STATUS_REG )
    #define PWM_1_STATUS_PTR            ((reg8 *)    PWM_1_PWMUDB_genblk8_stsreg__STATUS_REG )
    #define PWM_1_STATUS_MASK           (*(reg8 *)   PWM_1_PWMUDB_genblk8_stsreg__MASK_REG)
    #define PWM_1_STATUS_MASK_PTR       ((reg8 *)    PWM_1_PWMUDB_genblk8_stsreg__MASK_REG)
    #define PWM_1_STATUS_AUX_CTRL       (*(reg8 *)   PWM_1_PWMUDB_genblk8_stsreg__STATUS_AUX_CTL_REG)
    #define PWM_1_CONTROL               (*(reg8 *)   PWM_1_PWMUDB_genblk1_ctrlreg__CONTROL_REG)
    #define PWM_1_CONTROL_PTR           ((reg8 *)    PWM_1_PWMUDB_genblk1_ctrlreg__CONTROL_REG)


    /***********************************
    *          Constants
    ***********************************/

    /* Control Register bit definitions */
    #define PWM_1_CTRL_ENABLE_SHIFT      (0x07u)
    #define PWM_1_CTRL_RESET_SHIFT       (0x06u)
    #define PWM_1_CTRL_CMPMODE2_SHIFT    (0x03u)
    #define PWM_1_CTRL_CMPMODE1_SHIFT    (0x00u)
    #define PWM_1_CTRL_DEAD_TIME_SHIFT   (0x00u)   /* No Shift Needed for UDB block */
    
    /* Control Register Bit Masks */
    #define PWM_1_CTRL_ENABLE            (uint8)((uint8)0x01u << PWM_1_CTRL_ENABLE_SHIFT)
    #define PWM_1_CTRL_RESET             (uint8)((uint8)0x01u << PWM_1_CTRL_RESET_SHIFT)
    #define PWM_1_CTRL_CMPMODE2_MASK     (uint8)((uint8)0x07u << PWM_1_CTRL_CMPMODE2_SHIFT)
    #define PWM_1_CTRL_CMPMODE1_MASK     (uint8)((uint8)0x07u << PWM_1_CTRL_CMPMODE1_SHIFT)

    /* Status Register Bit Locations */
    #define PWM_1_STATUS_KILL_SHIFT          (0x05u)
    #define PWM_1_STATUS_FIFONEMPTY_SHIFT    (0x04u)
    #define PWM_1_STATUS_FIFOFULL_SHIFT      (0x03u)
    #define PWM_1_STATUS_TC_SHIFT            (0x02u)
    #define PWM_1_STATUS_CMP2_SHIFT          (0x01u)
    #define PWM_1_STATUS_CMP1_SHIFT          (0x00u)

    /* Status Register Interrupt Enable Bit Locations - UDB Status Interrupt Mask match Status Bit Locations*/
    #define PWM_1_STATUS_KILL_INT_EN_MASK_SHIFT          (PWM_1_STATUS_KILL_SHIFT)
    #define PWM_1_STATUS_FIFONEMPTY_INT_EN_MASK_SHIFT    (PWM_1_STATUS_FIFONEMPTY_SHIFT)
    #define PWM_1_STATUS_FIFOFULL_INT_EN_MASK_SHIFT      (PWM_1_STATUS_FIFOFULL_SHIFT)
    #define PWM_1_STATUS_TC_INT_EN_MASK_SHIFT            (PWM_1_STATUS_TC_SHIFT)
    #define PWM_1_STATUS_CMP2_INT_EN_MASK_SHIFT          (PWM_1_STATUS_CMP2_SHIFT)
    #define PWM_1_STATUS_CMP1_INT_EN_MASK_SHIFT          (PWM_1_STATUS_CMP1_SHIFT)

    /* Status Register Bit Masks */
    #define PWM_1_STATUS_KILL            (uint8)((uint8)0x00u << PWM_1_STATUS_KILL_SHIFT )
    #define PWM_1_STATUS_FIFOFULL        (uint8)((uint8)0x01u << PWM_1_STATUS_FIFOFULL_SHIFT)
    #define PWM_1_STATUS_FIFONEMPTY      (uint8)((uint8)0x01u << PWM_1_STATUS_FIFONEMPTY_SHIFT)
    #define PWM_1_STATUS_TC              (uint8)((uint8)0x01u << PWM_1_STATUS_TC_SHIFT)
    #define PWM_1_STATUS_CMP2            (uint8)((uint8)0x01u << PWM_1_STATUS_CMP2_SHIFT)
    #define PWM_1_STATUS_CMP1            (uint8)((uint8)0x01u << PWM_1_STATUS_CMP1_SHIFT)

    /* Status Register Interrupt Bit Masks  - UDB Status Interrupt Mask match Status Bit Locations */
    #define PWM_1_STATUS_KILL_INT_EN_MASK            (PWM_1_STATUS_KILL)
    #define PWM_1_STATUS_FIFOFULL_INT_EN_MASK        (PWM_1_STATUS_FIFOFULL)
    #define PWM_1_STATUS_FIFONEMPTY_INT_EN_MASK      (PWM_1_STATUS_FIFONEMPTY)
    #define PWM_1_STATUS_TC_INT_EN_MASK              (PWM_1_STATUS_TC)
    #define PWM_1_STATUS_CMP2_INT_EN_MASK            (PWM_1_STATUS_CMP2)
    #define PWM_1_STATUS_CMP1_INT_EN_MASK            (PWM_1_STATUS_CMP1)

    /* Datapath Auxillary Control Register bit definitions */
    #define PWM_1_AUX_CTRL_FIFO0_CLR         (0x01u)
    #define PWM_1_AUX_CTRL_FIFO1_CLR         (0x02u)
    #define PWM_1_AUX_CTRL_FIFO0_LVL         (0x04u)
    #define PWM_1_AUX_CTRL_FIFO1_LVL         (0x08u)
    #define PWM_1_STATUS_ACTL_INT_EN_MASK    (0x10u) /* As defined for the ACTL Register */
#endif /* PWM_1_UsingFixedFunction */

#endif  /* CY_PWM_PWM_1_H */


/* [] END OF FILE */
