eakat2/Checkers-Playing-Robot/SPI_Testing/test.py

import spidev
import RPi.GPIO as GPIO

class MCP23S17(object):
    """This class provides an abstraction of the GPIO expander MCP23S17
    for the Raspberry Pi.
    It is depndent on the Python packages spidev, which can
    be get from https://pypi.python.org/pypi/spidev.
    """
    DIR_INPUT = 1
    DIR_OUTPUT = 0
    PULLUP_ENABLED = 1
    PULLUP_DISABLED = 0
    LEVEL_LOW = 0
    LEVEL_HIGH = 1

    """Register addresses (ICON.BANK = 0) as documentined in the technical data sheet at
    http://ww1.microchip.com/downloads/en/DeviceDoc/21952b.pdf
    """
    MCP23S17_IODIRA = 0x00
    MCP23S17_IODIRB = 0x01
    MCP23S17_IPOLA = 0x02
    MCP23S17_IPOLB = 0x03
    MCP23S17_GPIOA = 0x12
    MCP23S17_GPIOB = 0x13
    MCP23S17_OLATA = 0x14
    MCP23S17_OLATB = 0x15
    MCP23S17_IOCON = 0x0A
    MCP23S17_GPPUA = 0x0C
    MCP23S17_GPPUB = 0x0D

    """Bit field flags as documentined in the technical data sheet at
    http://ww1.microchip.com/downloads/en/DeviceDoc/21952b.pdf
    """
    IOCON_UNUSED = 0x01
    IOCON_INTPOL = 0x02
    IOCON_ODR = 0x04
    IOCON_HAEN = 0x08
    IOCON_DISSLW = 0x10
    IOCON_SEQOP = 0x20
    IOCON_MIRROR = 0x40
    IOCON_BANK_MODE = 0x80

    IOCON_INIT = 0x00 # IOCON_BANK_MODE = 0, IOCON_HAEN = 0 address pins disabled

    MCP23S17_CMD_WRITE = 0x40
    MCP23S17_CMD_READ = 0x41

    def __init__(self, bus=0, ce=0, deviceID=0x00):
        """Constructor
        Initializes all attributes with 0.
        Keyword arguments:
        bus -- The SPI bus number
        ce -- The chip-enable number for the SPI
        deviceID -- The device ID of the component, i.e., the hardware address (default 0.0)
        """
        self.spi = spidev.SpiDev()
        print("Configured device: " + str(deviceID))
        self.bus = bus
        self.ce = ce
        self.deviceID = deviceID
        self._GPIOA = 0x00
        self._GPIOB = 0x00
        self._IODIRA = 0xFF
        self._IODIRB = 0xFF
        self._GPPUA = 0x00
        self._GPPUB = 0x00
        self.isInitialized = False

    def open(self):
        """Initializes the MCP23S17 with hardware-address access
        and sequential operations mode.
        """
        self.spi.open(self.bus, self.ce)
        self.spi.max_speed_hz = 10000000
        self.isInitialized = True

        self._writeRegister(MCP23S17.MCP23S17_IOCON, MCP23S17.IOCON_INIT)

    def close(self):
        """Closes the SPI connection that the MCP23S17 component is using.
        """
        self.spi.close()
        self.isInitialized = False

    def setDirection(self, pin, direction):
        """Sets the direction for a given pin.
        Parameters:
        pin -- The pin index (0 - 15)
        direction -- The direction of the pin (MCP23S17.DIR_INPUT, MCP23S17.DIR_OUTPUT)
        """
        assert (pin < 16)
        assert ((direction == MCP23S17.DIR_INPUT)
                or (direction == MCP23S17.DIR_OUTPUT))
        assert(self.isInitialized)

        if (pin < 8):
            register = MCP23S17.MCP23S17_IODIRA
            data = self._IODIRA
            noshifts = pin
        else:
            register = MCP23S17.MCP23S17_IODIRB
            noshifts = pin & 0x07
            data = self._IODIRB

        if (direction == MCP23S17.DIR_INPUT):
            data |= (1 << noshifts)
        else:
            data &= (~(1 << noshifts))

        self._writeRegister(register, data)

        if (pin < 8):
            self._IODIRA = data
        else:
            self._IODIRB = data

    def digitalWrite(self, pin, level):
        """Sets the level of a given pin.
        Parameters:
        pin -- The pin idnex (0 - 15)
        level -- The logical level to be set (MCP23S17.LEVEL_LOW, MCP23S17.LEVEL_HIGH)
        """
        assert(self.isInitialized)
        assert(pin < 16)
        assert((level == MCP23S17.LEVEL_HIGH) or (level == MCP23S17.LEVEL_LOW))

        if (pin < 8):
            register = MCP23S17.MCP23S17_GPIOA
            data = self._GPIOA
            noshifts = pin
        else:
            register = MCP23S17.MCP23S17_GPIOB
            noshifts = pin & 0x07
            data = self._GPIOB

        if (level == MCP23S17.LEVEL_HIGH):
            data |= (1 << noshifts)
        else:
            data &= (~(1 << noshifts))

        self._writeRegister(register, data)

        if (pin < 8):
            self._GPIOA = data
        else:
            self._GPIOB = data

    def _writeRegister(self, register, value):
        assert(self.isInitialized)
        command = MCP23S17.MCP23S17_CMD_WRITE | ((self.deviceID) << 1)
        self.spi.xfer2([command, register, value])

    def readRegister(self, register):
        assert(self.isInitialized)
        command = MCP23S17.MCP23S17_CMD_READ | ((self.deviceID) << 1)
        data = self.spi.xfer2([command, register, 0])
        return data[2]


import time, signal, sys

# Signal handler in order to exit the program properly
def signal_handler(signal, frame):
    print("\nSIGINT detected, exiting the program right now.")
    sys.exit(0)

signal.signal(signal.SIGINT, signal_handler)

# Creating instance
mcp = MCP23S17(ce=0, deviceID=0x00)
mcp.open()

# Setting outputs
mcp.setDirection(0, mcp.DIR_INPUT)
mcp.setDirection(1, mcp.DIR_INPUT)
mcp.setDirection(2, mcp.DIR_INPUT)
mcp.setDirection(3, mcp.DIR_INPUT)
mcp.setDirection(4, mcp.DIR_INPUT)
mcp.setDirection(5, mcp.DIR_INPUT)
mcp.setDirection(6, mcp.DIR_INPUT)
mcp.setDirection(7, mcp.DIR_INPUT)
mcp.setDirection(8, mcp.DIR_INPUT)
mcp.setDirection(9, mcp.DIR_INPUT)
mcp.setDirection(10, mcp.DIR_INPUT)
mcp.setDirection(11, mcp.DIR_INPUT)
mcp.setDirection(12, mcp.DIR_INPUT)
mcp.setDirection(13, mcp.DIR_INPUT)
mcp.setDirection(14, mcp.DIR_INPUT)
mcp.setDirection(15, mcp.DIR_INPUT)

# Blinking a led on the output
print(mcp.readRegister(0x12))

mcp.close()
print("We are done at this point!")
